adi04jan/ESP32-Programmable-Power-Supply/Images/image-1.png

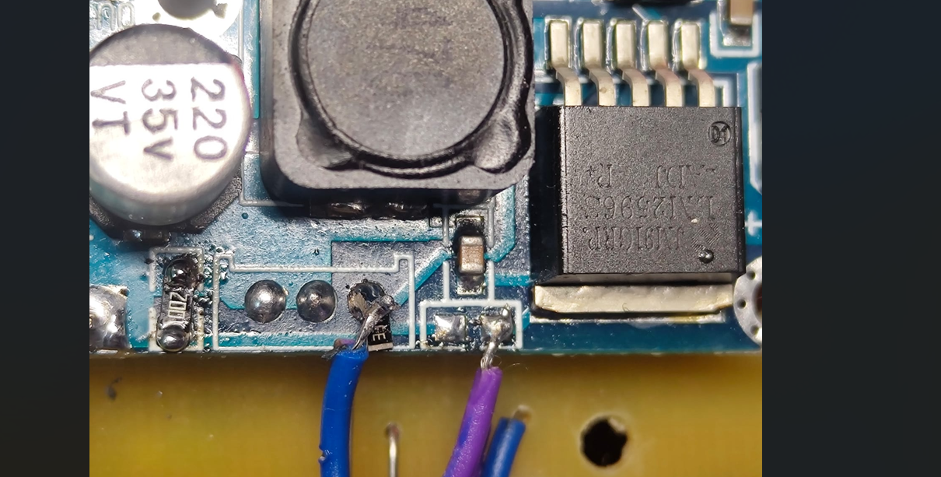
Images/image-1.png
