adi04jan/ESP32-Programmable-Power-Supply/Images/image-2.png

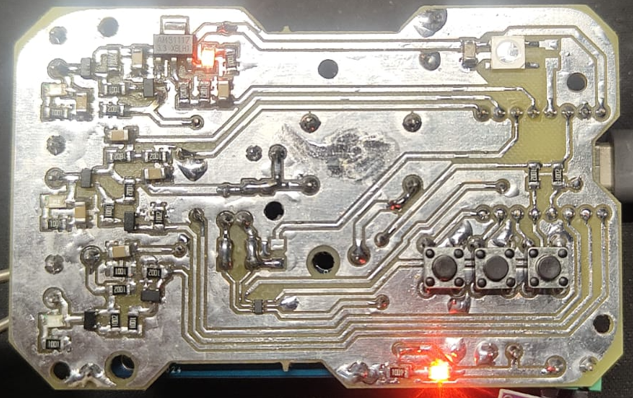
Images/image-2.png
