adi04jan/ESP32-Programmable-Power-Supply/Images/image-3.png

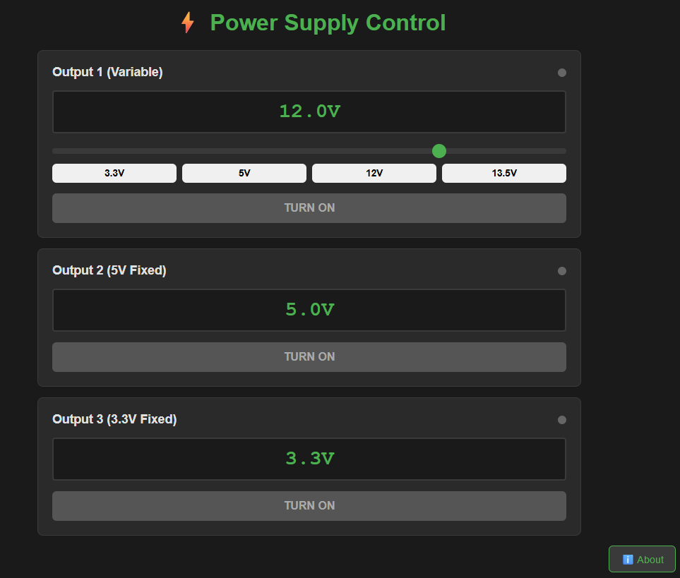
Images/image-3.png
