adi04jan/ESP32-Programmable-Power-Supply/Images/image-4.png

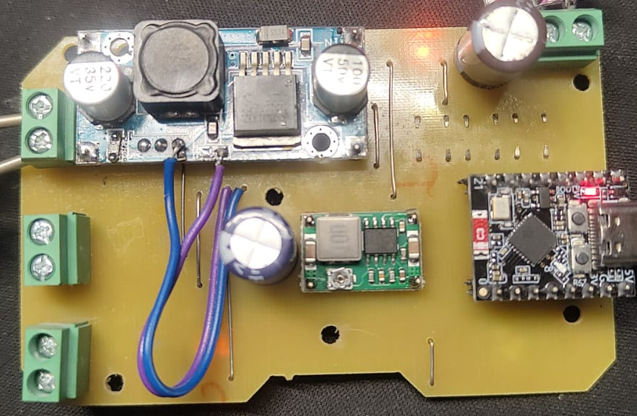
Images/image-4.png
