adi04jan/ESP32-Programmable-Power-Supply/ESP32_power_supply/web_page.h

#pragma once
const uint8_t index_html_gz[] PROGMEM = {
  0x1f, 0x8b, 0x08, 0x00, 0x00, 0x00, 0x00, 0x00, 0x00, 0x0a, 0xe4, 0xbd, 0xdb, 0x92, 0xdb, 0x48,
  0x96, 0x20, 0xf8, 0x9e, 0x66, 0xf9, 0x0f, 0x9e, 0x90, 0x32, 0x45, 0xa6, 0x40, 0x10, 0x20, 0x23,
  0x42, 0x21, 0x86, 0x18, 0x6a, 0xa5, 0x2e, 0x29, 0x75, 0xe9, 0x36, 0x92, 0x52, 0x59, 0x65, 0x5a,
  0x4d, 0xa6, 0x13, 0x70, 0x92, 0xa8, 0x00, 0x01, 0x14, 0x00, 0x92, 0x11, 0x19, 0x19, 0x6d, 0xf5,
  0x34, 0x2f, 0xf3, 0xd6, 0xd6, 0xef, 0x6b, 0xb6, 0x0f, 0xf3, 0x0b, 0xf3, 0xb2, 0x4f, 0xf3, 0x01,
  0xfb, 0x11, 0xf5, 0x03, 0xbb, 0x9f, 0xb0, 0x76, 0xce, 0x71, 0x77, 0x38, 0x2e, 0xbc, 0x84, 0xa4,
  0xec, 0x6e, 0xb3, 0x51, 0x56, 0x49, 0x04, 0xe0, 0xd7, 0xe3, 0xc7, 0x8f, 0x9f, 0xbb, 0xdf, 0xfb,
  0x26, 0x48, 0xfc, 0xe2, 0x22, 0x15, 0x6c, 0x5e, 0x2c, 0xa2, 0xd3, 0xaf, 0xbf, 0xba, 0x07, 0xff,
  0xb2, 0x88, 0xc7, 0xb3, 0xb1, 0x25, 0x62, 0x0b, 0xdf, 0x08, 0x1e, 0xc0, 0xbf, 0x0b, 0x51, 0x70,
  0xe6, 0xcf, 0x79, 0x96, 0x8b, 0x62, 0x6c, 0x2d, 0x8b, 0x69, 0xef, 0xd8, 0x62, 0x7d, 0xfd, 0x25,
  0xe6, 0x0b, 0x31, 0xb6, 0x56, 0xa1, 0x58, 0xa7, 0x49, 0x56, 0x58, 0xcc, 0x4f, 0xe2, 0x42, 0xc4,
  0xc5, 0xd8, 0x5a, 0x87, 0x41, 0x31, 0x1f, 0x07, 0x62, 0x15, 0xfa, 0xa2, 0x87, 0x0f, 0x76, 0x18,
  0x87, 0x45, 0xc8, 0xa3, 0x5e, 0xee, 0xf3, 0x48, 0x8c, 0x3d, 0x5b, 0xd5, 0xea, 0x4d, 0xc3, 0x62,
  0xec, 0x27, 0x2b, 0x91, 0x35, 0x5b, 0x2e, 0xe6, 0x62, 0x21, 0x7a, 0x7e, 0x12, 0x25, 0x99, 0xd1,
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
  0x39, 0x60, 0xe9, 0x65, 0xfd, 0xf3, 0x12, 0x26, 0x16, 0x85, 0x58, 0xa6, 0x8e, 0x4e, 0x8f, 0x44,
  0x1e, 0xce, 0x62, 0x56, 0x24, 0x67, 0x22, 0xce, 0xd9, 0xf5, 0xd1, 0x69, 0x94, 0x25, 0x49, 0x81,
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
};
const size_t index_html_gz_len = 24838;
